cnobile2012/VoltageCurrentMeter/sketchbooks/BatteryCharger/Roboto_Mono_Bold_15.h

// Created by http://oleddisplay.squix.ch/ Consider a donation
// In case of problems make sure that you are using the font file with the correct version!

const uint8_t Roboto_Mono_Bold_15Bitmaps[] PROGMEM = {
	// Bitmap Data:
	0x00, // ' '
	0xEC,0xCC,0xC4,0x40,0x04,0xE0, // '!'
	0xDB,0x69,0x24, // '"'
	0x1A,0x09,0x04,0x8F,0xE7,0xF1,0xA3,0xFD,0xFE,0x24,0x16,0x1B,0x00, // '#'
	0x10,0x18,0x7E,0xE6,0xC6,0xE0,0x78,0x1E,0x06,0xC6,0xC6,0x7E,0x18,0x10, // '$'
	0x70,0x34,0x8D,0x63,0x50,0x7C,0x02,0x01,0xF0,0x56,0x25,0x81,0x60,0x70, // '%'
	0x38,0x3E,0x13,0x09,0x87,0x83,0x83,0xCD,0xB6,0xCE,0x7F,0x1F,0xC0, // '&'
	0xDB,0x60, // '''
	0x21,0x91,0x8C,0x42,0x10,0x84,0x31,0x84,0x30,0xC0, // '('
	0x82,0x18,0x63,0x18,0x42,0x10,0x8C,0x62,0x33,0x00, // ')'
	0x18,0x0C,0x34,0x8F,0xE1,0x81,0x61,0x98, // '*'
	0x30,0x30,0x30,0xFE,0xFE,0x30,0x30,0x30, // '+'
	0xDB,0x68, // ','
	0xFD,0xF8, // '-'
	0x4E,0xE0, // '.'
	0x1C,0x30,0x61,0x83,0x06,0x18,0x30,0x61,0x83,0x00, // '/'
	0x38,0x7C,0xC6,0xC6,0xCE,0xDE,0xE6,0xC6,0xC6,0x7C,0x38, // '0'
	0x08,0xEF,0xA6,0x18,0x61,0x86,0x18,0x61,0x80, // '1'
	0x78,0xFC,0xC6,0xC6,0x0C,0x1C,0x18,0x30,0x60,0xFE,0xFE, // '2'
	0x7C,0xFE,0xC6,0x06,0x3C,0x3C,0x06,0x06,0xC6,0xFE,0x78, // '3'
	0x06,0x07,0x07,0x83,0xC3,0x61,0x31,0x99,0xFE,0x7F,0x03,0x01,0x80, // '4'
	0x7E,0x7E,0xC0,0xC0,0xFC,0xFE,0x06,0x06,0xC6,0xFE,0x78, // '5'
	0x18,0x78,0x60,0xC0,0xFC,0xFE,0xC6,0xC6,0xC6,0x7C,0x38, // '6'
	0xFE,0xFE,0x0C,0x0C,0x0C,0x18,0x18,0x30,0x30,0x60,0x60, // '7'
	0x78,0xFC,0xC6,0xC6,0x7C,0x7C,0xC6,0xC6,0xC6,0xFE,0x78, // '8'
	0x78,0xFC,0xC6,0xC6,0xC6,0xCE,0xFE,0x36,0x0C,0x78,0x70, // '9'
	0x4E,0xE0,0x00,0x4E,0xE0, // ':'
	0x4E,0xE0,0x00,0x06,0x66,0x64, // ';'
	0x06,0x1E,0xF8,0xC0,0x78,0x1E,0x02, // '<'
	0xFE,0xFE,0x00,0xFE,0xFE, // '='
	0xC0,0xF0,0x3C,0x06,0x3C,0xF0,0x80, // '>'
	0x3C,0x7E,0xC6,0x06,0x0E,0x0C,0x18,0x18,0x00,0x10,0x38, // '?'
	0x1E,0x08,0xC4,0x11,0x3C,0xD5,0xB5,0x6F,0x53,0xD4,0x5F,0x18,0x03,0xC0, // '@'
	0x0C,0x07,0x01,0xC0,0x58,0x36,0x0D,0x83,0x31,0xFC,0x7F,0x18,0xEE,0x18, // 'A'
	0xFC,0x7F,0x31,0x98,0xCC,0x67,0xE3,0xF9,0x8E,0xC7,0x7F,0x3F,0x00, // 'B'
	0x3C,0x7E,0xC6,0xC6,0xC0,0xC0,0xC0,0xC0,0xC6,0xFE,0x3C, // 'C'
	0xF8,0xFC,0xC6,0xC6,0xC6,0xC6,0xC6,0xC6,0xC6,0xFC,0xF8, // 'D'
	0xFE,0xFE,0xC0,0xC0,0xC0,0xFE,0xFE,0xC0,0xC0,0xFE,0xFE, // 'E'
	0xFE,0xFE,0xC0,0xC0,0xC0,0xFE,0xFE,0xC0,0xC0,0xC0,0xC0, // 'F'
	0x3C,0x7E,0xC6,0xC0,0xC0,0xDE,0xDE,0xC6,0xC6,0x7E,0x3C, // 'G'
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
};
const GFXglyph Roboto_Mono_Bold_15Glyphs[] PROGMEM = {
// bitmapOffset, width, height, xAdvance, xOffset, yOffset
	  {     0,   1,   1,  10,    0,    0 }, // ' '
	  {     1,   4,  11,  10,    3,  -11 }, // '!'
	  {     7,   6,   4,  10,    2,  -11 }, // '"'
	  {    10,   9,  11,  10,    0,  -11 }, // '#'
	  {    23,   8,  14,  10,    1,  -12 }, // '$'
	  {    37,  10,  11,  10,    0,  -11 }, // '%'
	  {    51,   9,  11,  10,    1,  -11 }, // '&'
	  {    64,   3,   4,  10,    3,  -11 }, // '''
	  {    66,   5,  15,  10,    3,  -12 }, // '('
	  {    76,   5,  15,  10,    2,  -12 }, // ')'
	  {    86,   9,   7,  10,    1,   -9 }, // '*'
	  {    94,   8,   8,  10,    1,   -9 }, // '+'
	  {   102,   3,   5,  10,    3,   -2 }, // ','
	  {   104,   7,   2,  10,    2,   -6 }, // '-'
	  {   106,   4,   3,  10,    3,   -3 }, // '.'
	  {   108,   7,  11,  10,    2,  -11 }, // '/'
	  {   118,   8,  11,  10,    1,  -11 }, // '0'
	  {   129,   6,  11,  10,    1,  -11 }, // '1'
	  {   138,   8,  11,  10,    1,  -11 }, // '2'
	  {   149,   8,  11,  10,    1,  -11 }, // '3'
	  {   160,   9,  11,  10,    0,  -11 }, // '4'
	  {   173,   8,  11,  10,    1,  -11 }, // '5'
	  {   184,   8,  11,  10,    1,  -11 }, // '6'
	  {   195,   8,  11,  10,    1,  -11 }, // '7'
	  {   206,   8,  11,  10,    1,  -11 }, // '8'
	  {   217,   8,  11,  10,    1,  -11 }, // '9'
	  {   228,   4,   9,  10,    3,   -9 }, // ':'
	  {   233,   4,  12,  10,    3,   -9 }, // ';'
	  {   239,   8,   7,  10,    1,   -8 }, // '<'
	  {   246,   8,   5,  10,    1,   -7 }, // '='
	  {   251,   8,   7,  10,    1,   -8 }, // '>'
	  {   258,   8,  11,  10,    1,  -11 }, // '?'
	  {   269,  10,  11,  10,    0,  -11 }, // '@'
	  {   283,  10,  11,  10,    0,  -11 }, // 'A'
	  {   297,   9,  11,  10,    1,  -11 }, // 'B'
	  {   310,   8,  11,  10,    1,  -11 }, // 'C'
	  {   321,   8,  11,  10,    1,  -11 }, // 'D'
	  {   332,   8,  11,  10,    1,  -11 }, // 'E'
	  {   343,   8,  11,  10,    1,  -11 }, // 'F'
	  {   354,   8,  11,  10,    1,  -11 }, // 'G'
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
};

const GFXfont Roboto_Mono_Bold_15 PROGMEM = {
    (uint8_t  *)Roboto_Mono_Bold_15Bitmaps,
    (GFXglyph *)Roboto_Mono_Bold_15Glyphs,
    0x20, 0x7E, 18};
