cnobile2012/VoltageCurrentMeter/sketchbooks/BatteryCharger/Roboto_Mono_Bold_16.h

// Created by http://oleddisplay.squix.ch/ Consider a donation
// In case of problems make sure that you are using the font file with the
// correct version!

const uint8_t Roboto_Mono_Bold_16Bitmaps[] PROGMEM = {
	// Bitmap Data:
	0x00, // ' '
	0x66,0x66,0x66,0x66,0x00,0xE6, // '!'
	0xDB,0x6D,0xB6, // '"'
	0x1B,0x06,0xC1,0x21,0xFE,0x7F,0x84,0x83,0x63,0xFC,0xFF,0x09,0x02,0x40,0xB0, // '#'
	0x08,0x04,0x0F,0x0F,0xC6,0x77,0x19,0x80,0xF0,0x3E,0x07,0x00,0xD8,0x6E,0x73,0xF0,0x60,0x30, // '$'
	0x70,0x3E,0x0D,0xB3,0xE8,0x74,0x03,0x00,0xB0,0x7E,0x14,0x89,0x20,0x78,0x0E, // '%'
	0x38,0x1F,0x06,0xC1,0xB0,0x78,0x0C,0x07,0xB3,0x6C,0xCF,0x33,0x8F,0xF1,0xEE, // '&'
	0xAA, // '''
	0x11,0x98,0xCC,0x63,0x18,0xC6,0x31,0x8C,0x31,0x86,0x10, // '('
	0x43,0x06,0x0C,0x30,0x61,0x86,0x18,0x61,0x86,0x30,0xC6,0x30,0x80, // ')'
	0x18,0x0C,0x12,0x5F,0xE1,0xC0,0xE0,0xD8,0xCC, // '*'
	0x18,0x0C,0x06,0x03,0x0F,0xF7,0xF8,0x60,0x30,0x18,0x00, // '+'
	0x66,0xCC,0xC0, // ','
	0xFE,0xFE, // '-'
	0x6E,0x60, // '.'
	0x0C,0x38,0x60,0xC1,0x86,0x0C,0x18,0x60,0xC1,0x86,0x0C,0x00, // '/'
	0x3C,0x3F,0x39,0x98,0xCC,0x76,0x7B,0xDD,0xCE,0xC6,0x73,0x1F,0x87,0x80, // '0'
	0x08,0xEF,0xB6,0x18,0x61,0x86,0x18,0x61,0x86, // '1'
	0x3C,0x7F,0x31,0x98,0xC0,0x60,0x70,0x70,0x70,0x30,0x30,0x3F,0xDF,0xE0, // '2'
	0x3C,0x7F,0x31,0x80,0xC0,0x61,0xE0,0xF8,0x0C,0x07,0x63,0x3F,0x8F,0x80, // '3'
	0x06,0x03,0x80,0xE0,0x78,0x36,0x0D,0x86,0x63,0xFE,0x7F,0x81,0x80,0x60,0x18, // '4'
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
	  {   406,   9,  12,  11,    1,  -12 }, // 'F'
	  {   420,   9,  12,  11,    1,  -12 }, // 'G'
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
};

const GFXfont Roboto_Mono_Bold_16 PROGMEM = {
    (uint8_t  *)Roboto_Mono_Bold_16Bitmaps,
    (GFXglyph *)Roboto_Mono_Bold_16Glyphs,
    0x20, 0x7E, 19};
